BlackBrix/TinyTOG/TinyTOG_NEW_with_ATtiny25/docs/Attiny-ISP/ATtiny_flasher_ISP.jpg

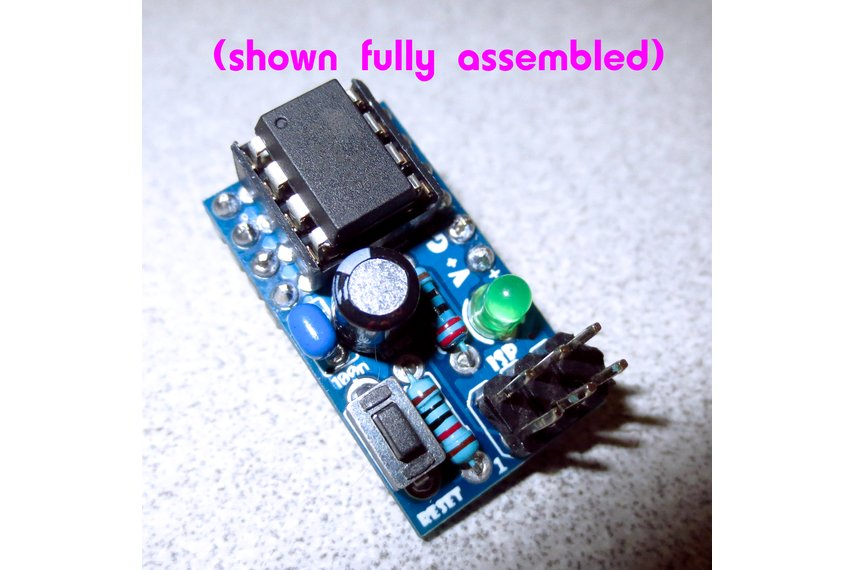
TinyTOG_NEW_with_ATtiny25/docs/Attiny-ISP/ATtiny_flasher_ISP.jpg
