BlackBrix/TinyTOG/TinyTOG_NEW_with_ATtiny25/firmware/flashing_with_atmel_studio/Fuses.png

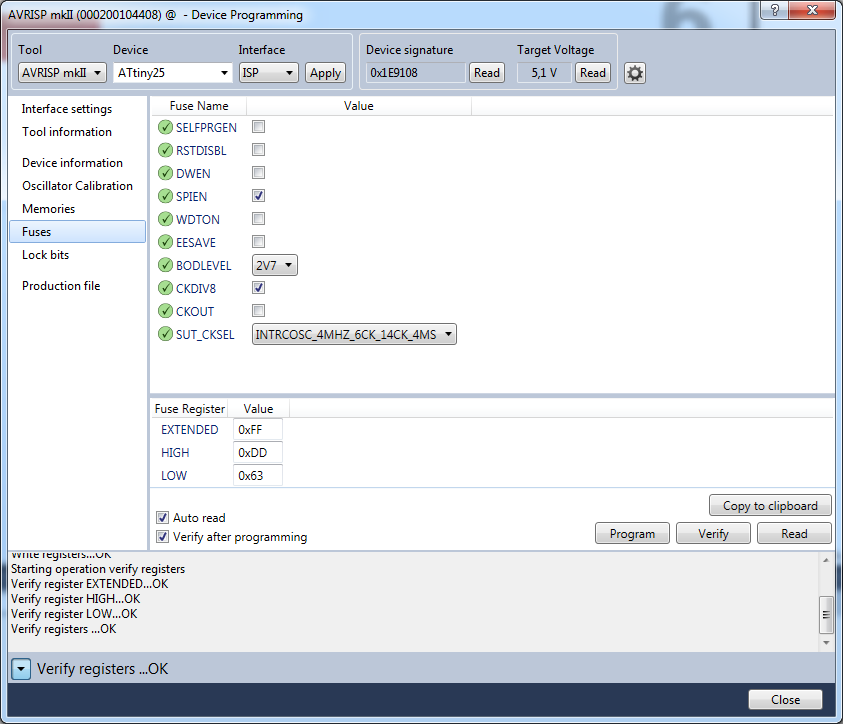
TinyTOG_NEW_with_ATtiny25/firmware/flashing_with_atmel_studio/Fuses.png
